zijn26/ESP32-DS-RV-26/image/{30CB05DD-FA60-430C-B2FF-0F3A6AF21A90}.png

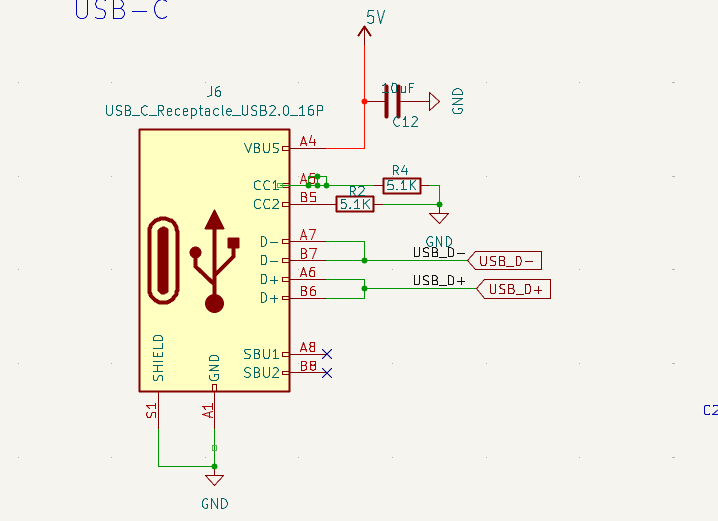
image/{30CB05DD-FA60-430C-B2FF-0F3A6AF21A90}.png
