zijn26/ESP32-DS-RV-26/image/{588B182C-2C22-4203-9883-5490EE00D111}.png

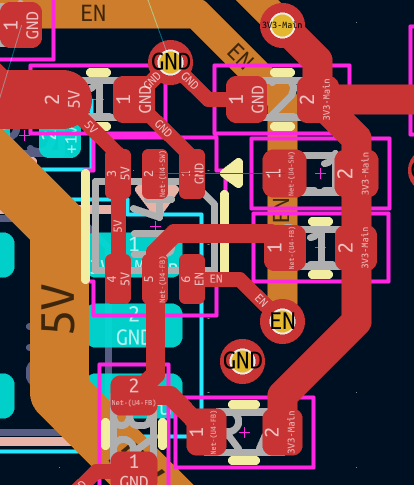
image/{588B182C-2C22-4203-9883-5490EE00D111}.png
