zijn26/ESP32-DS-RV-26/image/{3870F6FF-8E63-4B51-8C8F-186B9B9DBF1F}.png

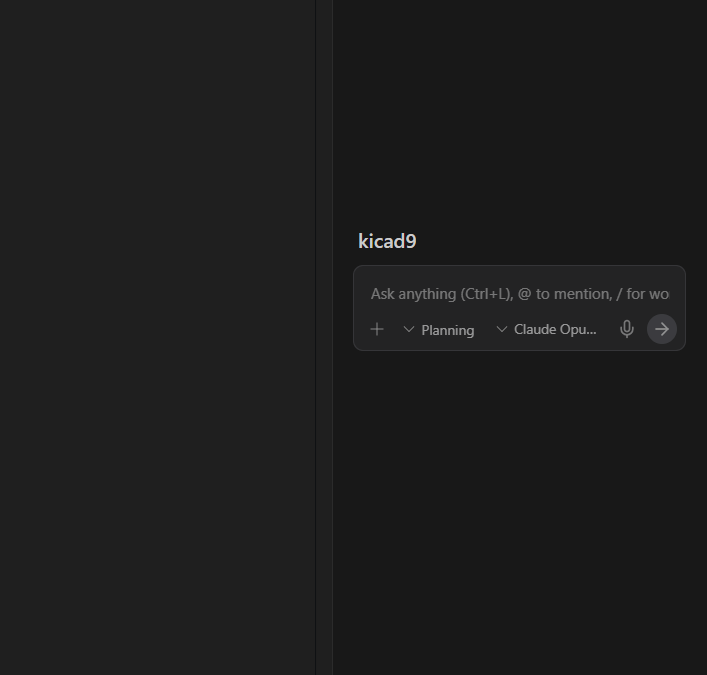
image/{3870F6FF-8E63-4B51-8C8F-186B9B9DBF1F}.png
