zijn26/ESP32-DS-RV-26/image/{AD39FE26-AC39-4C4F-855B-92879675BF7F}.png

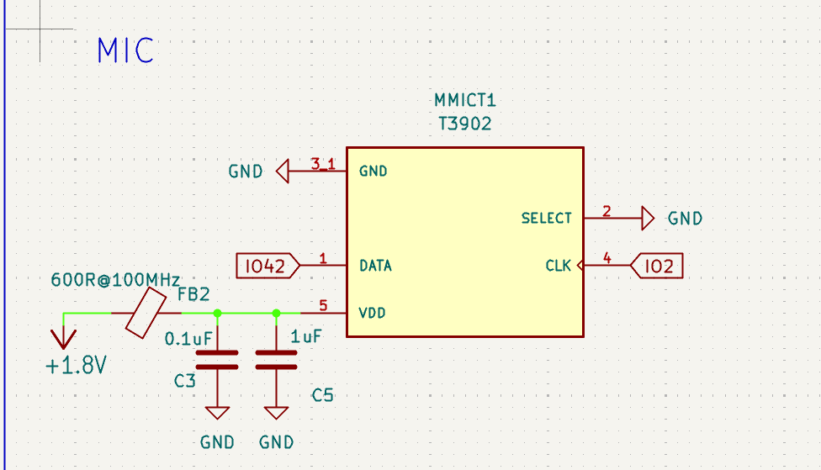
image/{AD39FE26-AC39-4C4F-855B-92879675BF7F}.png
