zijn26/ESP32-DS-RV-26/image/{BCBE2A39-BED5-4840-8F45-A99FD5698ECF}.png

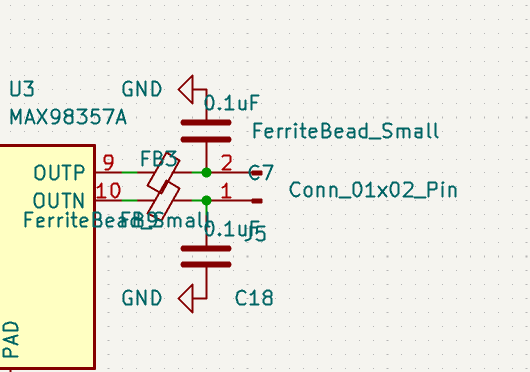
image/{BCBE2A39-BED5-4840-8F45-A99FD5698ECF}.png
